Boondock-Echo/Boondock-Hardware/Boondock-Echo/Assy, Boondock With Sidekick-A05/3DFiles/BE_CASE_RC02_ParametricButtonsAndSwitch.stl

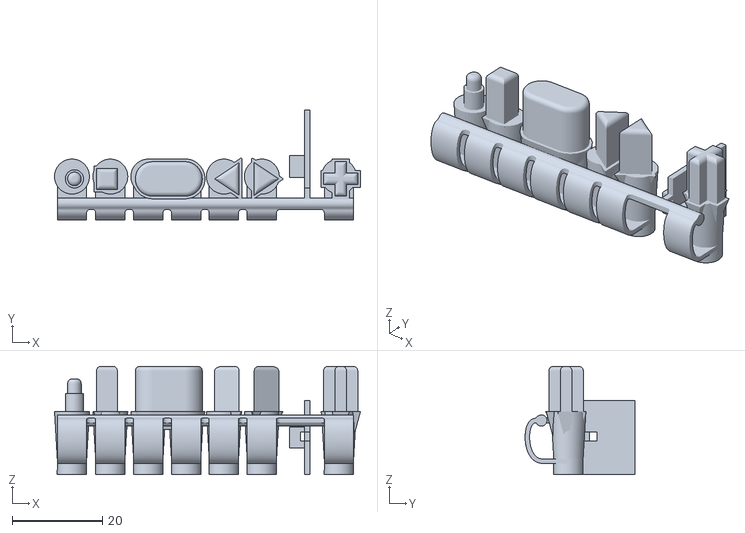
[picture p20: CAD file, 2024-09-01]
Boondock-Echo/Assy, Boondock With Sidekick-A05/3DFiles/BE_CASE_RC02_ParametricButtonsAndSwitch.stl
67.8 x 24.3 x 24.0
